villgzs/CurrentSensingByZMCT103C/KiCad/CurrentSensingByPCBandLM358.kicad_sch

## KiCad design KiCad/CurrentSensingByPCBandLM358.kicad_sch (2026-06-30)

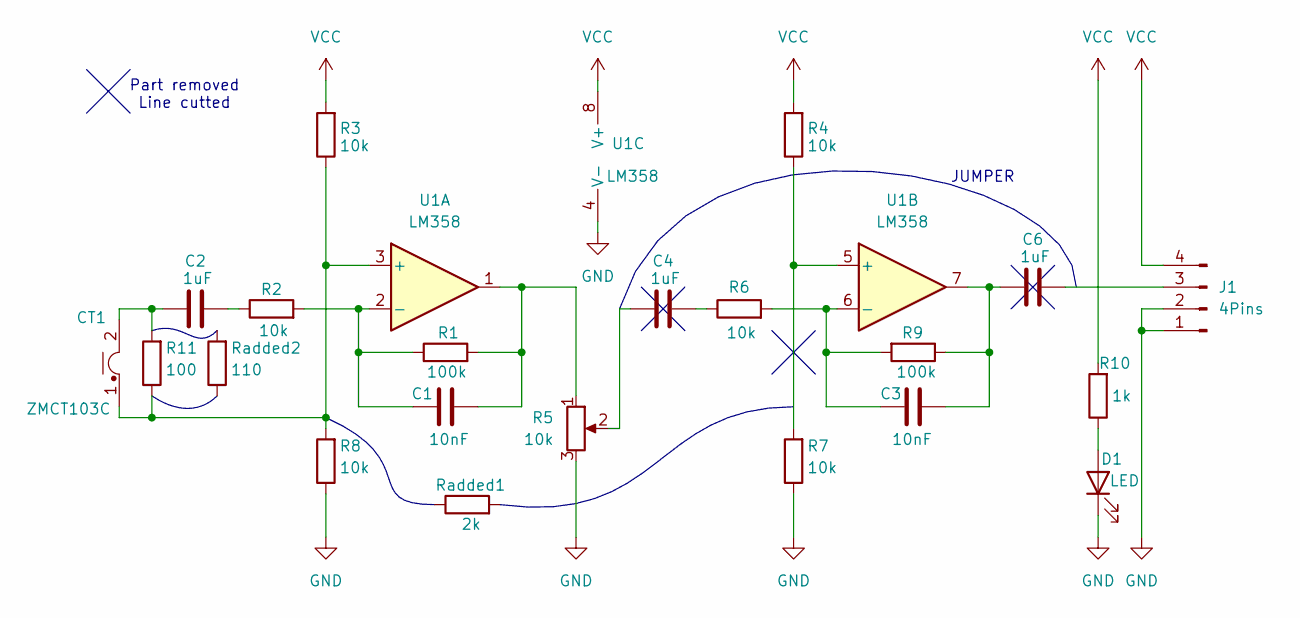
[picture p5: schematic CurrentSensingByPCBandLM358.kicad_sch]

Parts:
C1, C3: 10nF
C2, C4, C6: 1uF
CT1: ZMCT103C; Transformer_Zeming_ZMCT103C
D1: LED
J1: 4Pins
R1, R9: 100k
R2, R3, R4, R5, R6, R7, R8: 10k
R10: 1k
R11: 100
Radded1: 2k
Radded2: 110
U1: LM358

Connections:
GND: D1.1 (K), J1.1, J1.2, R5.3, R7.1, R8.1, U1.4 (V-)
unnamed: C1.1, R1.1, R2.2, U1.2 (-)
unnamed: C1.2, R1.2, R5.1, U1.1
unnamed: C2.1, CT1.2, R11.2
unnamed: C2.2, R2.1
unnamed: C3.1, C6.1, R9.1, U1.7
unnamed: C3.2, R6.2, R9.2, U1.6 (-)
unnamed: C4.1, R5.2
unnamed: C4.2, R6.1
unnamed: C6.2, J1.3
unnamed: CT1.1, R3.1, R8.2, R11.1, U1.3 (+)
unnamed: D1.2 (A), R10.1
unnamed: R4.1, R7.2, U1.5 (+)
VCC: J1.4, R3.2, R4.2, R10.2, U1.8 (V+)

Notes on the sheet:
Part removed Line cutted
JUMPER
